ShawnLulu/Dosyn/Printed Parts/1 Carriage.stl

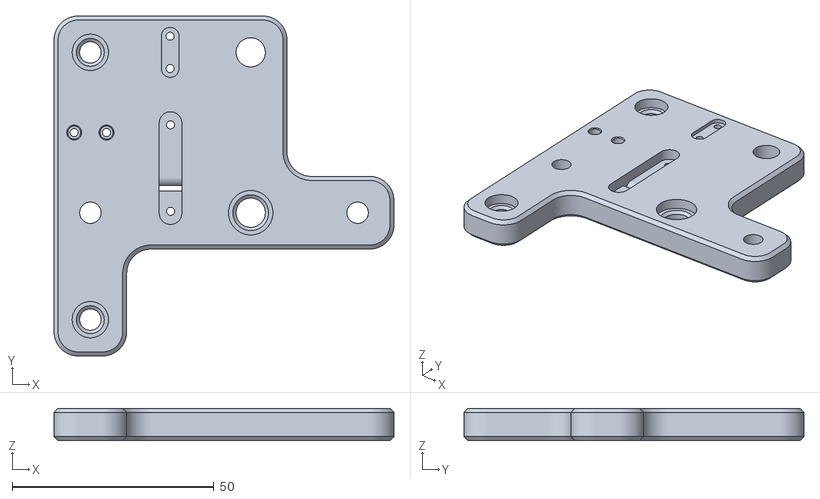
[picture p16: CAD file, 2023-11-30]
Printed Parts/1 Carriage.stl
84.2 x 84.2 x 8.00
