ShawnLulu/Dosyn/Printed Parts/1 Belt Clip.stl

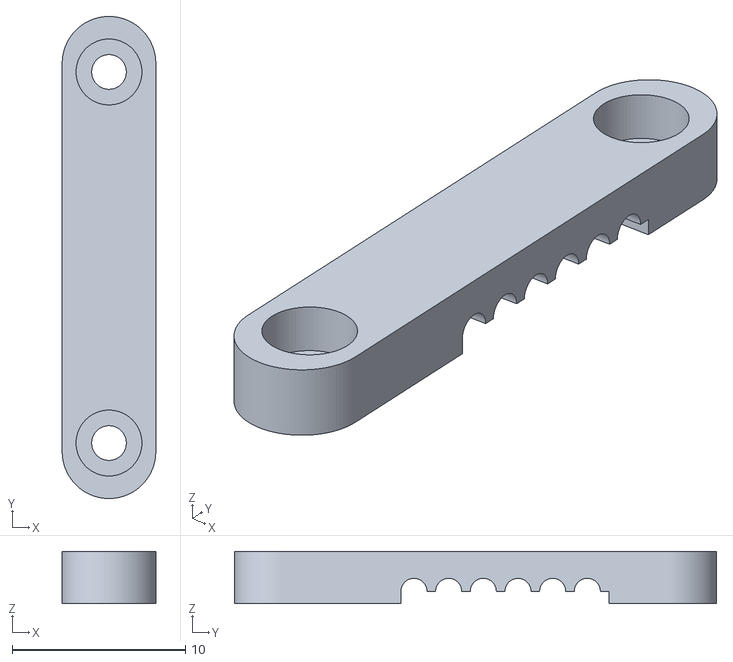
[picture p17: CAD file, 2023-11-30]
Printed Parts/1 Belt Clip.stl
5.40 x 27.8 x 3.00
