ShawnLulu/Dosyn/Printed Parts/1 Coutnterweight Lid.stl

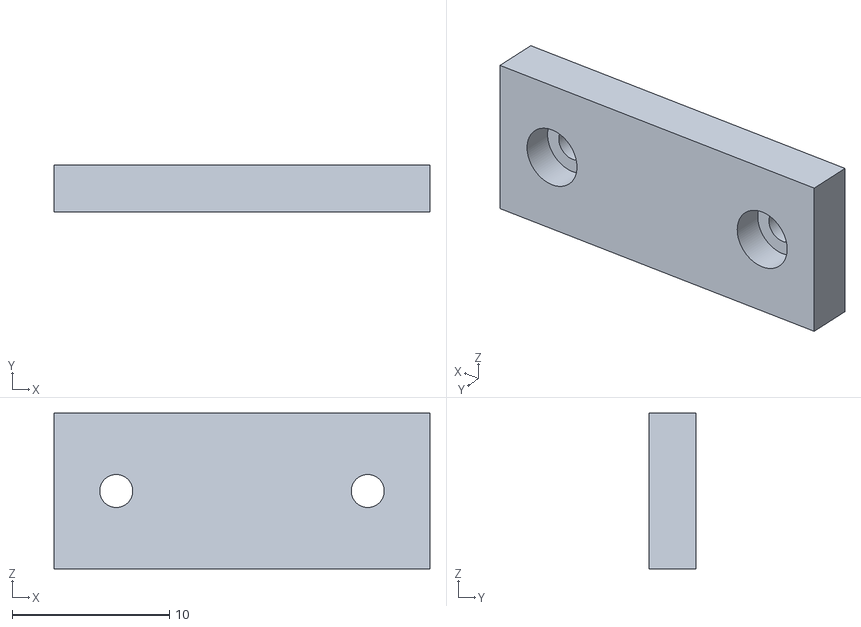
[picture p18: CAD file, 2023-11-30]
Printed Parts/1 Coutnterweight Lid.stl
23.9 x 3.00 x 9.92
