ShawnLulu/Dosyn/Printed Parts/1 Pulley Mount.stl

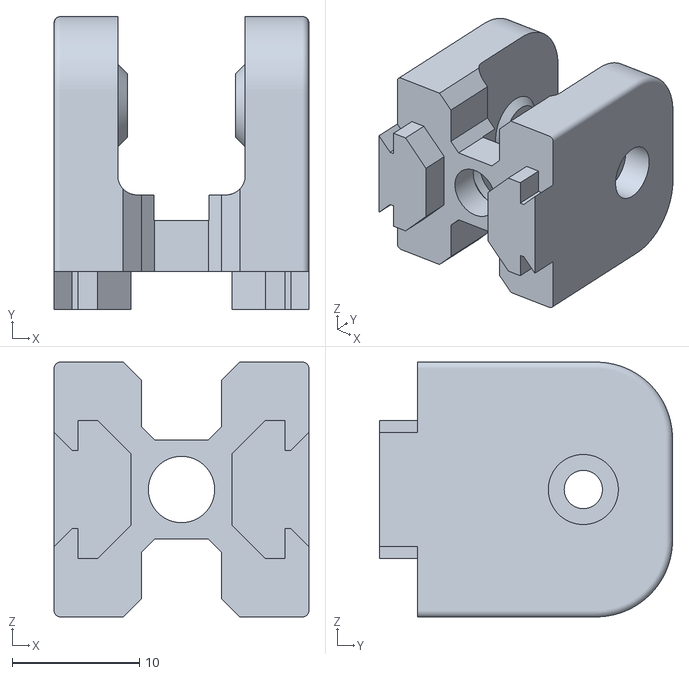
[picture p19: CAD file, 2023-11-30]
Printed Parts/1 Pulley Mount.stl
20.0 x 23.0 x 20.0
